devRCR/IntercambiadorGAMMA/Images/Anillo Sensores Detector/IMG_20240207_110916.jpg

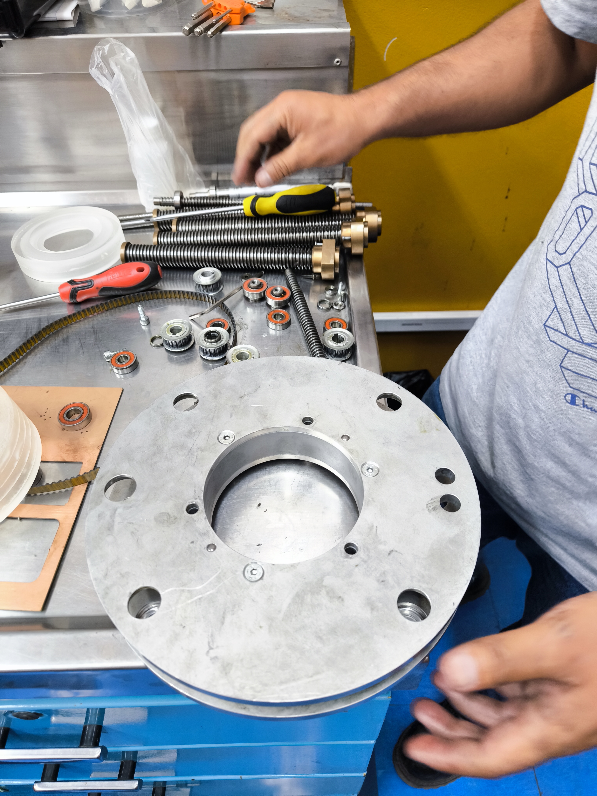
Images/Anillo Sensores Detector/IMG_20240207_110916.jpg
