devRCR/IntercambiadorGAMMA/Images/Anillo Sensores Detector/IMG_20240207_110922.jpg

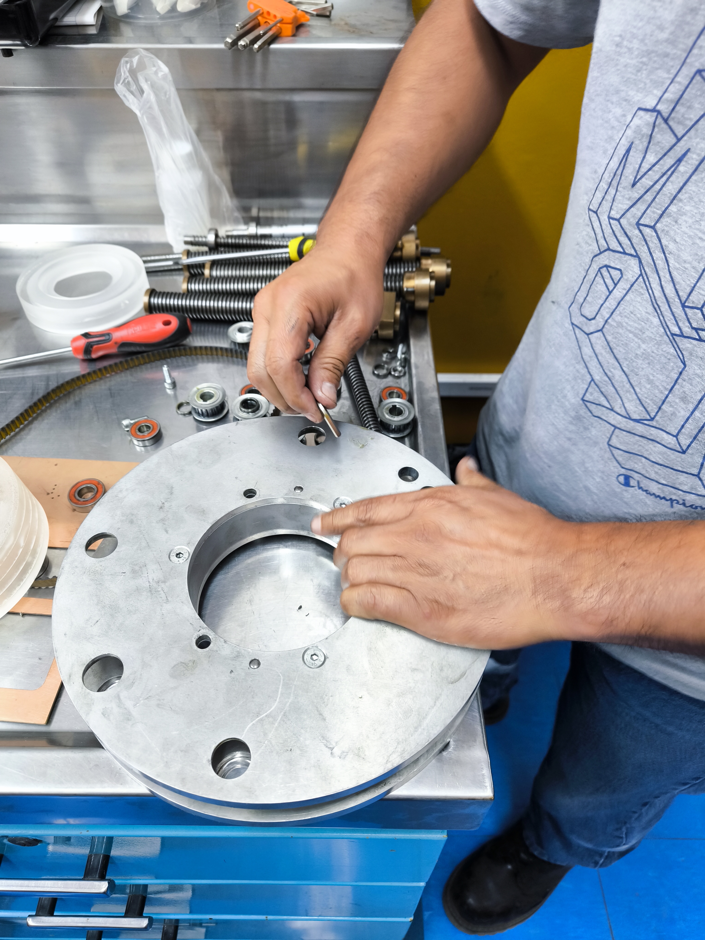
Images/Anillo Sensores Detector/IMG_20240207_110922.jpg
