devRCR/IntercambiadorGAMMA/Images/IMG_20240229_103801.jpg

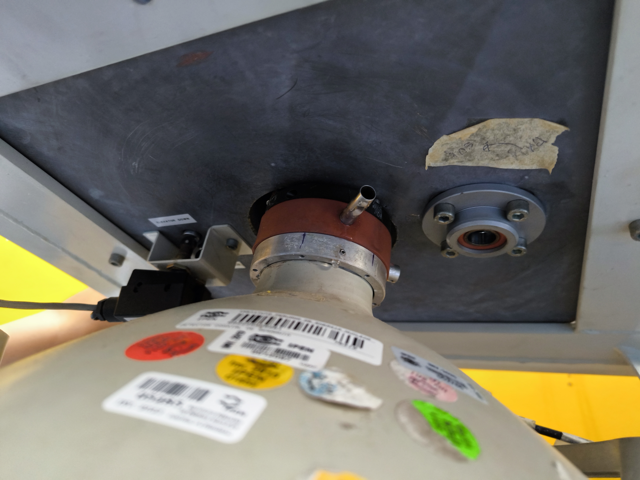
Images/IMG_20240229_103801.jpg
