devRCR/IntercambiadorGAMMA/Images/IMG_20240229_103802.jpg

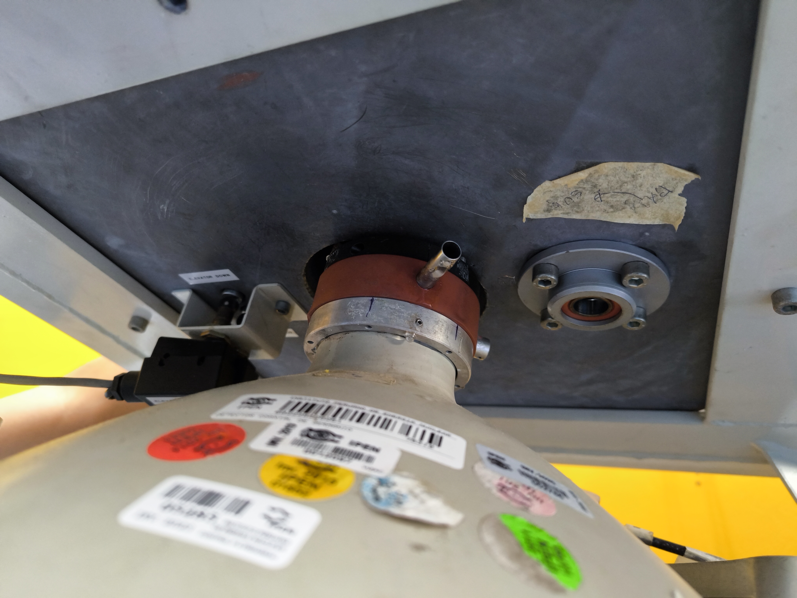
Images/IMG_20240229_103802.jpg
