devRCR/IntercambiadorGAMMA/Firmware/GAMMA_NodeSlave_Wheel/src/Hardware_NodeSlave_Wheel.h

// DEFINE LOS PUERTOS SERIALES
// ---------------------------
#define       SerialNodeMaster     Serial1

#define     RLY_DOOR_OPEN    46
#define     RLY_DOOR_CLOSE   47
#define     RLY_SAMPLE_NEXT  48
#define     RLY_B2_R04    49
#define     RLY_B2_R05    50
#define     RLY_B2_R06    51
#define     RLY_B2_R07    52
#define     RLY_B2_R08    53

#define     retardo   250

#define SENS_BLUE     10
#define SENS_GREEN     9
#define SENS_VIOLET    8
#define SENS_ORANGE    7

#define BTN_NEXT      3
#define BTN_CYCLE     4
#define BTN_UP        5
#define BTN_DOWN      6
#define BTN_OPEN     11
#define BTN_CLOSE    12

#define     SENSOR_TOP1     40  //A3
#define     SENSOR_TOP2     41  //A4
#define     SENSOR_BOTTOM1  42  //A5
#define     SENSOR_BOTTOM2  43  //A6

#define     BUZZER          A2  //4
#define     DRIVER_IN1      A1  //2
#define     DRIVER_IN2      A0  //3
#define     MOTOR_PWM        2  //5

#define     SPEED_HIGH     230
#define     SPEED_LOW      140

#define     SERIAL_NONE           1000
#define     SERIAL_STOP              0
#define     SERIAL_SAMPLE_NEXT     100
#define     SERIAL_SAMPLE_CYCLE    200
#define     SERIAL_DOOR_OPEN       300
#define     SERIAL_DOOR_CLOSE      400
#define     SERIAL_TABLE_DOWN      500
#define     SERIAL_TABLE_UP        600

#define       STATE_SAMPLE_NEXT       100
#define       STATE_SAMPLE_CYCLE      150
#define       STATE_SHIELD_CLOSE      200
#define       STATE_SHIELD_OPEN       250
#define       STATE_PLATE_DOWN        300
#define       STATE_PLATE_UP          350
